wojciechk8/NVMemProg-hardware/sim/pwr/pwr_sim_csen.cir

* gnetlist -g spice-sdb -o pwr_sim_csen.cir pwr_sim_csen.sch
*********************************************************
* Spice file generated by gnetlist                      *
* spice-sdb version 4.28.2007 by SDB --                 *
* provides advanced spice netlisting capability.        *
* Documentation at http://www.brorson.com/gEDA/SPICE/   *
*********************************************************
*vvvvvvvv  Included SPICE model from LM393.cir vvvvvvvv
* LM393 VOLTAGE COMPARATOR "MACROMODEL" SUBCIRCUIT
* CREATED USING PARTS VERSION 4.03 ON 03/07/90 AT 14:17
* REV (N/A)
* CONNECTIONS:   NON-INVERTING INPUT
*                | INVERTING INPUT
*                | | POSITIVE POWER SUPPLY
*                | | | NEGATIVE POWER SUPPLY
*                | | | | OPEN COLLECTOR OUTPUT
*                | | | | |
.SUBCKT LM393    1 2 3 4 5
*
  F1    9  3 V1 1
  IEE   3  7 DC 100.0E-6
  VI1  21  1 DC .75
  VI2  22  2 DC .75
  Q1    9 21  7 QIN
  Q2    8 22  7 QIN
  Q3    9  8  4 QMO
  Q4    8  8  4 QMI
.MODEL QIN PNP(IS=800.0E-18 BF=2.000E3)
.MODEL QMI NPN(IS=800.0E-18 BF=1002)
.MODEL QMO NPN(IS=800.0E-18 BF=1000 CJC=1E-15 TR=807.4E-9)
  E1   10  4  9  4  1
  V1   10 11 DC 0
  Q5    5 11  4 QOC
.MODEL QOC NPN(IS=800.0E-18 BF=20.29E3 CJC=1E-15 TF=942.6E-12 TR=543.8E-9)
  DP    4  3 DX
  RP 3  4 46.3E3
.MODEL DX  D(IS=800.0E-18)
*
.ENDS
*^^^^^^^^  End of included SPICE model from LM393.cir ^^^^^^^^
*
*vvvvvvvv  Included SPICE model from TS912.cir vvvvvvvv
** Standard Linear Ics Macromodels, 1993.
** CONNECTIONS :
* 1 NON-INVERTING INPUT
* 2 INVERTING INPUT
* 3 POSITIVE POWER SUPPLY
* 4 NEGATIVE POWER SUPPLY
* 5 OUTPUT
.SUBCKT TS912 2 1 4 5 3
**********************************************************
.MODEL MDTH D IS=1E-8 KF=6.563355E-14 CJO=10F
* INPUT STAGE
CIP 2 5 1.500000E-12
CIN 1 5 1.500000E-12
EIP 10 5 2 5 1
EIN 16 5 1 5 1
RIP 10 11 6.500000E+00
RIN 15 16 6.500000E+00
RIS 11 15 7.655100E+00
DIP 11 12 MDTH 400E-12
DIN 15 14 MDTH 400E-12
VOFP 12 13 DC 0.000000E+00
VOFN 13 14 DC 0
IPOL 13 5 4.000000E-05
CPS 11 15 3.82E-08
DINN 17 13 MDTH 400E-12
VIN 17 5 -0.5000000e+00
DINR 15 18 MDTH 400E-12
VIP 4 18 -0.5000000E+00
FCP 4 5 VOFP 7.750000E+00
FCN 5 4 VOFN 7.750000E+00
* AMPLIFYING STAGE
FIP 5 19 VOFP 5.500000E+02
FIN 5 19 VOFN 5.500000E+02
RG1 19 5 5.087344E+05
RG2 19 4 5.087344E+05
CC 19 29 2.200000E-08
HZTP 30 29 VOFP 12.33E+02
HZTN  5 30 VOFN 12.33E+02
DOPM 19 22 MDTH 400E-12
DONM 21 19 MDTH 400E-12
HOPM 22 28 VOUT 3135
VIPM 28 4 150
HONM 21 27 VOUT 3135
VINM 5 27 150
EOUT 26 23 19 5 1
VOUT 23 5 0
ROUT 26 3 65
COUT 3 5 1.000000E-12
DOP 19 68 MDTH 400E-12
VOP 4 25 1.924
HSCP 68 25 VSCP1 1E8
DON 69 19 MDTH 400E-12
VON 24 5 2.4419107
HSCN 24 69 VSCN1 1.5E8
VSCTHP 60 61 0.1375
DSCP1 61 63 MDTH 400E-12
VSCP1 63 64 0
ISCP 64 0 1.000000E-8
DSCP2 0 64 MDTH 400E-12
DSCN2 0 74 MDTH 400E-12
ISCN 74 0 1.000000E-8
VSCN1 73 74 0
DSCN1 71 73 MDTH 400E-12
VSCTHN 71 70 -0.75
ESCP 60 0 2 1 500
ESCN 70 0 2 1 -2000
.ENDS
*^^^^^^^^  End of included SPICE model from TS912.cir ^^^^^^^^
*
*==============  Begin SPICE netlist of main design ============
Vcset cset 0 DC 0.25
Vload ctrl_load 0 pwl 0ms 200 4ms 50
* begin vcvs expansion, e<name>
Eload LOAD 0 unconnected_pin-1 unconnected_pin-2 VALUE={i(Vout)*v(ctrl_load)}
Isense_Eload unconnected_pin-1 unconnected_pin-2 dc 0
IOut_Eload LOAD 0 dc 0
* end vcvs expansion
R4 DIFF_OUT 3 39k  
R2 0 2 39k  
XU1 2 3 VCC 0 DIFF_OUT TS912
Vout 1 LOAD DC 0V
R110 #OCPROT VCC 10k  
XU3 cset DIFF_OUT VCC 0 #OCPROT LM393
R3 3 1 1.2k  
R1 2 VCC 1.2k  
Rcs VCC 1 180m  
V2 VCC 0 DC 5V
.OPTIONS ABSTOL=1nA VNTOL=1uV CHGTOL=1pC ITL1=150 ITL2=150 ITL4=500 RELTOL=0.001

.CONTROL
  *OP
  TRAN 0.1u 4m uic
  PLOT V(cset) V(DIFF_OUT) I(Vout) V(#OCPROT)
  meas tran yeval FIND i(Vout) WHEN v(#OCPROT)=4.5 FALL=1
.ENDC

.end
