wojciechk8/NVMemProg-hardware/sim/pwr/pwr_sim_fpga_sw.cir

* gnetlist -g spice-sdb -o pwr_sim_fpga_sw.cir pwr_sim_fpga_sw.sch
*********************************************************
* Spice file generated by gnetlist                      *
* spice-sdb version 4.28.2007 by SDB --                 *
* provides advanced spice netlisting capability.        *
* Documentation at http://www.brorson.com/gEDA/SPICE/   *
*********************************************************
*vvvvvvvv  Included SPICE model from LM393.cir vvvvvvvv
* LM393 VOLTAGE COMPARATOR "MACROMODEL" SUBCIRCUIT
* CREATED USING PARTS VERSION 4.03 ON 03/07/90 AT 14:17
* REV (N/A)
* CONNECTIONS:   NON-INVERTING INPUT
*                | INVERTING INPUT
*                | | POSITIVE POWER SUPPLY
*                | | | NEGATIVE POWER SUPPLY
*                | | | | OPEN COLLECTOR OUTPUT
*                | | | | |
.SUBCKT LM393    1 2 3 4 5
*
  F1    9  3 V1 1
  IEE   3  7 DC 100.0E-6
  VI1  21  1 DC .75
  VI2  22  2 DC .75
  Q1    9 21  7 QIN
  Q2    8 22  7 QIN
  Q3    9  8  4 QMO
  Q4    8  8  4 QMI
.MODEL QIN PNP(IS=800.0E-18 BF=2.000E3)
.MODEL QMI NPN(IS=800.0E-18 BF=1002)
.MODEL QMO NPN(IS=800.0E-18 BF=1000 CJC=1E-15 TR=807.4E-9)
  E1   10  4  9  4  1
  V1   10 11 DC 0
  Q5    5 11  4 QOC
.MODEL QOC NPN(IS=800.0E-18 BF=20.29E3 CJC=1E-15 TF=942.6E-12 TR=543.8E-9)
  DP    4  3 DX
  RP 3  4 46.3E3
.MODEL DX  D(IS=800.0E-18)
*
.ENDS
*^^^^^^^^  End of included SPICE model from LM393.cir ^^^^^^^^
*
*vvvvvvvv  Included SPICE model from OptiMOS2_20V.lib vvvvvvvv

*****************************************************************
* INFINEON Power Transistors                                    *
* Level-1 / 3 SPICE Library for OptiMOS/OptiMOS2 n-Channel      *
* Transistors (20V)                                             *
* Version 240715                                                *
*                                                               *
*****************************************************************
*                                                               *
* The Simulation Model is subject to change without notice. In  *
* addition, models can be a useful tool in evaluating device    *
* performance, they cannot reflect the accurate device          *
* performance under all conditions, nor are they intended to    *
* replace bread boarding for final verification. Infineon       *
* therefore does not assume any warranty or liability           *
* whatsoever arising from their use. Infineon does not assume   *
* any warranty or liability for the values and functions of the *
* Simulation Model.                                             *
* The methods and results of the Simulation Model are to the    *
* best of our knowledge                                         *
* correct. However, the user is fully responsible to verify and *
* validate these results under the operating conditions and in  *
* the environment of its application. Infineon will not bear    *
* the responsibility arising out of or in connection with any   *
* malfunction of the Simulation Models.                         *
* Models provided by Infineon are not warranted by Infineon as  *
* completely and comprehensively representing all the           *
* specifications and operating characteristics of the           *
* semiconductor products to which these models relate. The      *
* models describe the characteristics of typical devices. In    *
* all cases, the current data sheet information for a given     *
* device is the conclusive design guideline and the only actual * 
* performance specification.                                    *
*                                                               *
*                                                               *
* This library contains models of the following INFINEON        *
* OptiMOS/OptiMOS2 transistors:                                 *
*                                                               *
*  OptiMOS2 20V ULL, 1.8 V rated                                *
* BSR802N                                                       *
* BSL802SN                                                      *
* BSL806N  (L3 modeled as single only)                          *
* BSS806N                                                       *
* BSS806NE                                                      *
* BSS816NW                                                      * 
* BSD816SN                                                      *
* BSD840N  (L3 modeled as single only)                          *
*                                                               *
*   OptiMOS2 20V SLL, (2.5 V rated)                             *
* BSC019N02KS                                                   *
* BSC026N02KS                                                   *
* BSC046N02KS                                                   *
* BSR202N                                                       *
* BSL202SN                                                      *
* BSO330N02K                                                    *
* BSL205N  (L3 modeled as single only)                          *
* BSL207N  (L3 modeled as single only)                          *
* BSL214N  (L3 modeled as single only)                          *
* BSS205N                                                       *
* BSS214N                                                       *
* BSS214NW                                                      *
* BSD235N  (L3 modeled as single only)                          *
* BSD214SN                                                      *
*                                                               *
*****************************************************************
* thermal nodes of level 3 models:                              *
*                                                               *
*  .SUBCKT IPP05N03LA drain gate source Tj Tcase                *
*  Tj :    potential=temperature (in ?C) at junction (typically *
*          not connected)                                       *
*  Tcase : node where the boundary contition - external heat    *
*          sinks etc - have to be connected (ideal heat sink    *
*          can be modeled by using a voltage source stating the *
*          ambient temperature in ?C between Tcase and ground.  *
*                                                               *
*****************************************************************

.SUBCKT S3_20_s_var dd g s0 Tj PARAMS: a=1 dVth=0 dR=0 dgfs=0 Inn=1 Unn=1 Rmax=1
+gmin=1 Rs=1 Rp=1 dC=0 Rm=1u heat=0

.PARAM  Fm=0.07      Fn=0.5       kbq=85.8u
.PARAM  c=1          muc=0.0      Vth0=1.628   auth=1.481m   al=0.5
.PARAM  UT=100m      ab=24.7m     ab2=0        lB=-23        UB=25.37

.PARAM  b0=128.9     p0=2.714     p1=-6.3m     p2=13u

.PARAM  Rd=8.3m      nmu=2.7      Tref=298     T0=273       lnIsj=-22.24
.PARAM  ndi=1.218    Rdi=6.36m    nmu2=0.032   ta=3n        td=20n
.PARAM  Rf=0.6       nmu3=1.5    

.PARAM  f1=380p      f2=400p      f3=830p      U0=3       nc=0.5    nd=0.5
.PARAM  g1=11        bb=0.4       remp=5p      f2r=100p

.PARAM  Vmin=1.378   Vmax=1.878  dCmax=0.33
.PARAM  Vth={Vth0+(Vmax-Vth0)*limit(dVth,0,1)-(Vmin-Vth0)*limit(dVth,-1,0)}
.PARAM  q0={b0*((T0/Tref)**nmu3)*a}
.PARAM  q1={(Unn-Inn*Rs-Vth0)*q0}
.PARAM  q2={(Fm*SQRT(0.4)-c)*Inn*q0}
.PARAM  Rlim={(q1+2*q2*Rmax-SQRT(q1**2+4*q2))/(2*q2)}
.PARAM  dRd={Rd/a+if(dVth==0,limit(dR,0,1)*max(Rlim-Rd/a-Rs-Rp,0),0)}
.PARAM  bm={c/((1/gmin-Rs)**2*Inn*a*(T0/Tref)**nmu3)}
.PARAM  bet={b0+(b0-bm)*if(dR==0,if(dVth==0,limit(dgfs,-1,0),0),0)}
.PARAM  dC1={1+dCmax*limit(dC,0,1)}
.PARAM  dC2={1+dCmax*limit(dC,0,1)*1.5}

.PARAM  Cox={f1*a*dC2}
.PARAM  Cox1={remp*SQRT(a)*dC2}
.PARAM  Cds0={(f2*a+f2r*SQRT(a))*dC1}
.PARAM  Cgs0={f3*a*dC1}
.PARAM  dRdi={Rdi/a}

.FUNC  I0(Uee,p,pp,z1,cc)  {if(Uee>pp,(Uee-cc*z1)*z1,p*(pp-p)/cc*exp((Uee-pp)/p))}
.FUNC  Ig(Uds,T,p,Uee,cc)  {bet*(T0/T)**nmu3*I0(Uee,p,min(2*p,p+cc*Uds),min(Uds,Uee/(2*cc)),cc)}
.FUNC  J(d,g,T,da,s) 
+ {a*s*((Ig(da,T,(p0+(p1+p2*T)*T)*kbq*T,g-Vth+auth*(T-Tref)+Fm*da**Fn,c*(T/Tref)**muc)+exp(min(lB+(d-UB-ab*(T-Tref))/UT,25))))}

.FUNC  Idiode(Usd,Tj,Iss) {exp(min(log(Iss)+Usd/(ndi*kbq*Tj),7))-Iss}
.FUNC  Idiod(Usd,Tj)      {a*Idiode(Usd,Tj,exp(min(lnIsj+(Tj/Tref-1)*1.12/(ndi*kbq*Tj),7))*(Tj/Tref)**1)}

E_Edg     d   ox  VALUE {max(V(d,g),-bb)-(1/(g1*(1-nc))*((1/(1+g1*max(V(d,g)+bb,0)))**(nc-1)-(1/(1+g1*bb))**(nc-1)))}
C_Cdg    ox    g  {Cox}
Vx        d   ox1 0
C_Cdg1   ox1   g  {Cox1}

E_Eds     d edep  VALUE {(V(d,s)-I(V_sense3)/Cds0)}
C_Cds  edep    s  {Cds0}

C_Cgs   g    s   {Cgs0}


G_chan    d    s  VALUE={J(V(d,s),V(g,s),T0+limit(V(Tj),-200,300),(SQRT(1+4*al*abs(V(d,s)))-1)/2/al,sgn(V(d,s)))}
G_RMos   d1    d  VALUE={V(d1,d)/(Rf*dRd+(1-Rf)*dRd*((limit(V(Tj),-200,999)+T0)/Tref)**nmu)}
V_sense  dd   d1  0
G_diode   s   d3  VALUE={Idiod(V(s,d3),T0+limit(V(Tj),-200,499))}
G_Rdio   d2   d1  VALUE={V(d2,d1)/(dRdi*((limit(V(Tj),-200,999)+T0)/Tref)**nmu2)}
V_sense2 d2   d3  0

L_L001    a    c  {td/(ta+td)}
R_R001    a    b  {1/ta}
V_sense3  c    0  0
E_E001    b    0  VALUE {I(V_sense2)}
E_E002    e    0  VALUE {Cds0*1/(1-nd)*U0**nd*(limit(U0+V(d1,s),0,2*UB))**(1-nd)}
R_R002    e    c  1
R_R003    a    0  500Meg

R1        g    s  1G
Rd01      d    s  500Meg
Rd02     d2    s  500Meg
Rd03     d1    d  1k

Rmet      s    s0 {Rm}

G_TH      0   Tj  VALUE =
+{(LIMIT(I(V_sense2)*V(d1,s)+(V(s,s0)**2)/Rm+(I(V_sense)-I(V_sense2))*V(d1,d)+
+(I(V_sense)-I(V_sense2)-I(E_Edg)-I(Vx)-I(E_Eds))*V(d,s),-10k,100k))}

.ENDS

**********

.SUBCKT S3_20_u_var dd g s0 Tj PARAMS: a=1 dVth=0 dR=0 dgfs=0 Inn=1 Unn=1 Rmax=1
+gmin=1 Rs=1 Rp=1 dC=0 Rm=1u heat=0

.PARAM  Fm=0.025     Fn=0.5       kbq=85.8u
.PARAM  c=0.75       muc=0.0      Vth0=1.17    auth=1.36m    al=0.001
.PARAM  UT=100m      ab=22m       ab2=0        lB=-23        UB=24.2

.PARAM  b0=180       p0=2.61      p1=-6.93m    p2=12.5u

.PARAM  Rd=6.642m    nmu=3.045    Tref=298     T0=273       lnIsj=-22.24
.PARAM  ndi=1.218    Rdi=6.36m    nmu2=0.032   ta=3n        td=20n
.PARAM  Rf=0.723     nmu3=1.5    

.PARAM  f1=700p      f2=400p      f3=970p      U0=3         nc=0.5    nd=0.5
.PARAM  g1=21        bb=0.11      remp=4p      f2r=100p

.PARAM  Vmin=0.97    Vmax=1.37    dCmax=0.33
.PARAM  Vth={Vth0+(Vmax-Vth0)*limit(dVth,0,1)-(Vmin-Vth0)*limit(dVth,-1,0)}
.PARAM  q0={b0*((T0/Tref)**nmu3)*a}
.PARAM  q1={(Unn-Inn*Rs-Vth0)*q0}
.PARAM  q2={(Fm*SQRT(0.4)-c)*Inn*q0}
.PARAM  Rlim={(q1+2*q2*Rmax-SQRT(q1**2+4*q2))/(2*q2)}
.PARAM  dRd={Rd/a+if(dVth==0,limit(dR,0,1)*max(Rlim-Rd/a-Rs-Rp,0),0)}
.PARAM  bm={c/((1/gmin-Rs)**2*Inn*a*(T0/Tref)**nmu3)}
.PARAM  bet={b0+(b0-bm)*if(dR==0,if(dVth==0,limit(dgfs,-1,0),0),0)}
.PARAM  dC1={1+dCmax*limit(dC,0,1)}
.PARAM  dC2={1+dCmax*limit(dC,0,1)*1.5}

.PARAM  Cox={f1*a*dC2}
.PARAM  Cox1={remp*SQRT(a)*dC2}
.PARAM  Cds0={(f2*a+f2r*SQRT(a))*dC1}
.PARAM  Cgs0={f3*a*dC1}
.PARAM  dRdi={Rdi/a}

.FUNC  I0(Uee,p,pp,z1,cc)  {if(Uee>pp,(Uee-cc*z1)*z1,p*(pp-p)/cc*exp((Uee-pp)/p))}
.FUNC  Ig(Uds,T,p,Uee,cc)  {bet*(T0/T)**nmu3*I0(Uee,p,min(2*p,p+cc*Uds),min(Uds,Uee/(2*cc)),cc)}
.FUNC  J(d,g,T,da,s) 
+ {a*s*((Ig(da,T,(p0+(p1+p2*T)*T)*kbq*T,g-Vth+auth*(T-Tref)+Fm*da**Fn,c*(T/Tref)**muc)+exp(min(lB+(d-UB-ab*(T-Tref))/UT,25))))}

.FUNC  Idiode(Usd,Tj,Iss) {exp(min(log(Iss)+Usd/(ndi*kbq*Tj),7))-Iss}
.FUNC  Idiod(Usd,Tj)      {a*Idiode(Usd,Tj,exp(min(lnIsj+(Tj/Tref-1)*1.12/(ndi*kbq*Tj),7))*(Tj/Tref)**1)}

E_Edg     d   ox  VALUE {max(V(d,g),-bb)-(1/(g1*(1-nc))*((1/(1+g1*max(V(d,g)+bb,0)))**(nc-1)-(1/(1+g1*bb))**(nc-1)))}
C_Cdg    ox    g  {Cox}
Vx        d   ox1 0
C_Cdg1   ox1   g  {Cox1}

E_Eds     d edep  VALUE {(V(d,s)-I(V_sense3)/Cds0)}
C_Cds  edep    s  {Cds0}

C_Cgs   g    s   {Cgs0}


G_chan    d    s  VALUE={J(V(d,s),V(g,s),T0+limit(V(Tj),-200,300),(SQRT(1+4*al*abs(V(d,s)))-1)/2/al,sgn(V(d,s)))}
G_RMos   d1    d  VALUE={V(d1,d)/(Rf*dRd+(1-Rf)*dRd*((limit(V(Tj),-200,999)+T0)/Tref)**nmu)}
V_sense  dd   d1  0
G_diode   s   d3  VALUE={Idiod(V(s,d3),T0+limit(V(Tj),-200,499))}
G_Rdio   d2   d1  VALUE={V(d2,d1)/(dRdi*((limit(V(Tj),-200,999)+T0)/Tref)**nmu2)}
V_sense2 d2   d3  0

L_L001    a    c  {td/(ta+td)}
R_R001    a    b  {1/ta}
V_sense3  c    0  0
E_E001    b    0  VALUE {I(V_sense2)}
E_E002    e    0  VALUE {Cds0*1/(1-nd)*U0**nd*(limit(U0+V(d1,s),0,2*UB))**(1-nd)}
R_R002    e    c  1
R_R003    a    0  500Meg

R1        g    s  1G
Rd01      d    s  500Meg
Rd02     d2    s  500Meg
Rd03     d1    d  1k

Rmet      s    s0 {Rm}

G_TH      0   Tj  VALUE =
+{(LIMIT(I(V_sense2)*V(d1,s)+(V(s,s0)**2)/Rm+(I(V_sense)-I(V_sense2))*V(d1,d)+
+(I(V_sense)-I(V_sense2)-I(E_Edg)-I(Vx)-I(E_Eds))*V(d,s),-10k,100k))}

.ENDS

****************************************************************************************************

.SUBCKT BSC019N02KS drain gate source Tj Tcase PARAMS: dVth=0 dRdson=0 dgfs=0 dC=0 Zthtype=0 Ls=1n Ld=1n Lg=3n

.PARAM Rs=482u      Rg=1.9       Rd=50u       Rm=400u
.PARAM Inn=50       Unn=4.5      Rmax=1.95m   gmin=100

.PARAM act=11.03



X1  d1 g s Tj S3_20_s_var PARAMS: a={act} dVth={dVth} dR={dRdson} dgfs={dgfs} Inn={Inn} Unn={Unn} 
                                        +Rmax={Rmax} gmin={gmin} Rs={Rs} Rp={Rd} dC={dC} Rm={Rm}
Rg    g1     g    {Rg}   
Lg    gate   g1   {Lg*if(dgfs==99,0,1)}
Gs    s1     s    VALUE={V(s1,s)/(Rs*(1+(limit(V(Tj),-200,999)-25)*4m)-Rm)}
Rsa   s1     s    1Meg
Ls    source s1   {Ls*if(dgfs==99,0,1)}
Rda   d1     d2   {Rd}
Ld    drain  d2   {Ld*if(dgfs==99,0,1)}
RLs   source s1   10
RLg   gate   g1   10
RLd   drain  d2   10




Rth1  Tj      t1              {2.39m+limit(Zthtype,0,1)*878.98u}
Rth2  t1      t2              {32.13m+limit(Zthtype,0,1)*11.89m}
Rth3  t2      t3              {123.34m+limit(Zthtype,0,1)*39.62m}
Rth4  t3      t4              {129.59m+limit(Zthtype,0,1)*217.61m}
Rth5  t4      Tcase           {239.83m+limit(Zthtype,0,1)*402.72m}
Cth1  Tj      0               76.781u
Cth2  t1      0               435.464u
Cth3  t2      0               2.72m
Cth4  t3      0               1.944m
Cth5  t4      0               47.017m
Cth6  Tcase   0               30m

.ENDS

**********

.SUBCKT BSC026N02KS drain gate source Tj Tcase PARAMS: dVth=0 dRdson=0 dgfs=0 dC=0 Zthtype=0 Ls=1n Ld=1n Lg=3n

.PARAM Rs=361u      Rg=1.5       Rd=50u       Rm=190u
.PARAM Inn=50       Unn=4.5      Rmax=2.6m    gmin=57

.PARAM act=6.77



X1  d1 g s Tj S3_20_s_var PARAMS: a={act} dVth={dVth} dR={dRdson} dgfs={dgfs} Inn={Inn} Unn={Unn} 
                                        +Rmax={Rmax} gmin={gmin} Rs={Rs} Rp={Rd} dC={dC} Rm={Rm}
Rg    g1     g    {Rg}   
Lg    gate   g1   {Lg*if(dgfs==99,0,1)}
Gs    s1     s    VALUE={V(s1,s)/(Rs*(1+(limit(V(Tj),-200,999)-25)*4m)-Rm)}
Rsa   s1     s    1Meg
Ls    source s1   {Ls*if(dgfs==99,0,1)}
Rda   d1     d2   {Rd}
Ld    drain  d2   {Ld*if(dgfs==99,0,1)}
RLs   source s1   10
RLg   gate   g1   10
RLd   drain  d2   10




Rth1  Tj      t1              {3.89m+limit(Zthtype,0,1)*1.44m}
Rth2  t1      t2              {51.65m+limit(Zthtype,0,1)*19.11m}
Rth3  t2      t3              {186.29m+limit(Zthtype,0,1)*64.8m}
Rth4  t3      t4              {211.13m+limit(Zthtype,0,1)*300.99m}
Rth5  t4      Tcase           {313.61m+limit(Zthtype,0,1)*447.09m}
Cth1  Tj      0               47.127u
Cth2  t1      0               270.877u
Cth3  t2      0               1.834m
Cth4  t3      0               1.193m
Cth5  t4      0               33.557m
Cth6  Tcase   0               35m

.ENDS

**********

.SUBCKT BSC046N02KS drain gate source Tj Tcase PARAMS: dVth=0 dRdson=0 dgfs=0 dC=0 Zthtype=0 Ls=1n Ld=1n Lg=3n

.PARAM Rs=254u      Rg=1.9       Rd=50u       Rm=83u
.PARAM Inn=50       Unn=4.5      Rmax=4.6m    gmin=42

.PARAM act=3.55



X1  d1 g s Tj S3_20_s_var PARAMS: a={act} dVth={dVth} dR={dRdson} dgfs={dgfs} Inn={Inn} Unn={Unn} 
                                        +Rmax={Rmax} gmin={gmin} Rs={Rs} Rp={Rd} dC={dC} Rm={Rm}
Rg    g1     g    {Rg}   
Lg    gate   g1   {Lg*if(dgfs==99,0,1)}
Gs    s1     s    VALUE={V(s1,s)/(Rs*(1+(limit(V(Tj),-200,999)-25)*4m)-Rm)}
Rsa   s1     s    1Meg
Ls    source s1   {Ls*if(dgfs==99,0,1)}
Rda   d1     d2   {Rd}
Ld    drain  d2   {Ld*if(dgfs==99,0,1)}
RLs   source s1   10
RLg   gate   g1   10
RLd   drain  d2   10




Rth1  Tj      t1              {7.41m+limit(Zthtype,0,1)*2.75m}
Rth2  t1      t2              {96.23m+limit(Zthtype,0,1)*35.61m}
Rth3  t2      t3              {343.77m+limit(Zthtype,0,1)*124.41m}
Rth4  t3      t4              {402.63m+limit(Zthtype,0,1)*574.54m}
Rth5  t4      Tcase           {417.25m+limit(Zthtype,0,1)*595.4m}
Cth1  Tj      0               24.712u
Cth2  t1      0               145.39u
Cth3  t2      0               1.004m
Cth4  t3      0               625.577u
Cth5  t4      0               25.139m
Cth6  Tcase   0               40m

.ENDS

**********

.SUBCKT BSR202N drain gate source Tj Tcase PARAMS: dVth=0 dRdson=0 dgfs=0 dC=0 Zthtype=0 Ls=0.8n Ld=1n Lg=3n

.PARAM Rs=4.48m     Rg=1.9       Rd=500u      Rm=4m
.PARAM Inn=3.8      Unn=4.5      Rmax=23m     gmin=8

.PARAM act=0.991



X1  d1 g s Tj S3_20_s_var PARAMS: a={act} dVth={dVth} dR={dRdson} dgfs={dgfs} Inn={Inn} Unn={Unn} 
                                        +Rmax={Rmax} gmin={gmin} Rs={Rs} Rp={Rd} dC={dC} Rm={Rm}
Rg    g1     g    {Rg}   
Lg    gate   g1   {Lg*if(dgfs==99,0,1)}
Gs    s1     s    VALUE={V(s1,s)/(Rs*(1+(limit(V(Tj),-200,999)-25)*4m)-Rm)}
Rsa   s1     s    1Meg
Ls    source s1   {Ls*if(dgfs==99,0,1)}
Rda   d1     d2   {Rd}
Ld    drain  d2   {Ld*if(dgfs==99,0,1)}
RLs   source s1   10
RLg   gate   g1   10
RLd   drain  d2   10




Rth1  Tj      t1              {26.69m+limit(Zthtype,0,1)*9.88m}
Rth2  t1      t2              {321.74m+limit(Zthtype,0,1)*119.08m}
Rth3  t2      t3              {1.48+limit(Zthtype,0,1)*451.64m}
Rth4  t3      t4              {42.78+limit(Zthtype,0,1)*37.73}
Rth5  t4      Tcase           {30.33+limit(Zthtype,0,1)*26.75}
Cth1  Tj      0               6.864u
Cth2  t1      0               43.483u
Cth3  t2      0               141.188u
Cth4  t3      0               1.166m
Cth5  t4      0               9.189m
Cth6  Tcase   0               5m

.ENDS

**********

.SUBCKT BSL202SN drain gate source Tj Tcase PARAMS: dVth=0 dRdson=0 dgfs=0 dC=0 Zthtype=0 Ls=1n Ld=1n Lg=3n

.PARAM Rs=5.48m     Rg=1.9       Rd=140u      Rm=5m
.PARAM Inn=3.8      Unn=4.5      Rmax=24m     gmin=8

.PARAM act=0.991



X1  d1 g s Tj S3_20_s_var PARAMS: a={act} dVth={dVth} dR={dRdson} dgfs={dgfs} Inn={Inn} Unn={Unn} 
                                        +Rmax={Rmax} gmin={gmin} Rs={Rs} Rp={Rd} dC={dC} Rm={Rm}
Rg    g1     g    {Rg}   
Lg    gate   g1   {Lg*if(dgfs==99,0,1)}
Gs    s1     s    VALUE={V(s1,s)/(Rs*(1+(limit(V(Tj),-200,999)-25)*4m)-Rm)}
Rsa   s1     s    1Meg
Ls    source s1   {Ls*if(dgfs==99,0,1)}
Rda   d1     d2   {Rd}
Ld    drain  d2   {Ld*if(dgfs==99,0,1)}
RLs   source s1   10
RLg   gate   g1   10
RLd   drain  d2   10




Rth1  Tj      t1              {26.56m+limit(Zthtype,0,1)*9.83m}
Rth2  t1      t2              {320.25m+limit(Zthtype,0,1)*118.52m}
Rth3  t2      t3              {1.93+limit(Zthtype,0,1)*459.59m}
Rth4  t3      t4              {10.69+limit(Zthtype,0,1)*11.84}
Rth5  t4      Tcase           {11.67+limit(Zthtype,0,1)*12.93}
Cth1  Tj      0               6.898u
Cth2  t1      0               43.687u
Cth3  t2      0               145.816u
Cth4  t3      0               635.538u
Cth5  t4      0               7m


.ENDS

*********************


.SUBCKT BSL205N drain gate source Tj Tcase PARAMS: dVth=0 dRdson=0 dgfs=0 dC=0 Zthtype=0 Ls=1n Ld=0.5n Lg=2n

.PARAM Rs=7.13m     Rg=4.9       Rd=550u      Rm=600u
.PARAM Inn=2.5      Unn=4.5      Rmax=50m     gmin=4.6

.PARAM act=0.361



X1  d1 g s Tj S3_20_s_var PARAMS: a={act} dVth={dVth} dR={dRdson} dgfs={dgfs} Inn={Inn} Unn={Unn} 
                                        +Rmax={Rmax} gmin={gmin} Rs={Rs} Rp={Rd} dC={dC} Rm={Rm}
Rg    g1     g    {Rg}   
Lg    gate   g1   {Lg*if(dgfs==99,0,1)}
Gs    s1     s    VALUE={V(s1,s)/(Rs*(1+(limit(V(Tj),-200,999)-25)*4m)-Rm)}
Rsa   s1     s    1Meg
Ls    source s1   {Ls*if(dgfs==99,0,1)}
Rda   d1     d2   {Rd}
Ld    drain  d2   {Ld*if(dgfs==99,0,1)}
RLs   source s1   10
RLg   gate   g1   10
RLd   drain  d2   10




Rth1  Tj      t1              {72.91m+limit(Zthtype,0,1)*26.98m}
Rth2  t1      t2              {796.9m+limit(Zthtype,0,1)*294.92m}
Rth3  t2      t3              {4.09+limit(Zthtype,0,1)*1.28}
Rth4  t3      t4              {19.18+limit(Zthtype,0,1)*7.1}
Rth5  t4      Tcase           {49.02+limit(Zthtype,0,1)*18.14}
Cth1  Tj      0               2.513u
Cth2  t1      0               6.514u
Cth3  t2      0               50.593u
Cth4  t3      0               214.138u
Cth5  t4      0               1.193m
Cth6  Tcase   0               5m

.ENDS

**********

.SUBCKT BSS205N drain gate source Tj Tcase PARAMS: dVth=0 dRdson=0 dgfs=0 dC=0 Zthtype=0 Ls=1n Ld=0.5n Lg=2n

.PARAM Rs=8.11m     Rg=4.9       Rd=550u      Rm=600u
.PARAM Inn=2.5      Unn=4.5      Rmax=50m     gmin=4.6

.PARAM act=0.361



X1  d1 g s Tj S3_20_s_var PARAMS: a={act} dVth={dVth} dR={dRdson} dgfs={dgfs} Inn={Inn} Unn={Unn} 
                                        +Rmax={Rmax} gmin={gmin} Rs={Rs} Rp={Rd} dC={dC} Rm={Rm}
Rg    g1     g    {Rg}   
Lg    gate   g1   {Lg*if(dgfs==99,0,1)}
Gs    s1     s    VALUE={V(s1,s)/(Rs*(1+(limit(V(Tj),-200,999)-25)*4m)-Rm)}
Rsa   s1     s    1Meg
Ls    source s1   {Ls*if(dgfs==99,0,1)}
Rda   d1     d2   {Rd}
Ld    drain  d2   {Ld*if(dgfs==99,0,1)}
RLs   source s1   10
RLg   gate   g1   10
RLd   drain  d2   10




Rth1  Tj      t1              {72.91m+limit(Zthtype,0,1)*26.98m}
Rth2  t1      t2              {796.9m+limit(Zthtype,0,1)*294.92m}
Rth3  t2      t3              {4.09+limit(Zthtype,0,1)*1.28}
Rth4  t3      t4              {11.88+limit(Zthtype,0,1)*11.21}
Rth5  t4      Tcase           {56.78+limit(Zthtype,0,1)*53.57}
Cth1  Tj      0               2.513u
Cth2  t1      0               6.514u
Cth3  t2      0               50.593u
Cth4  t3      0               389.69u
Cth5  t4      0               600u
Cth6  Tcase   0               6m

.ENDS

**********

.SUBCKT BSL207N drain gate source Tj Tcase PARAMS: dVth=0 dRdson=0 dgfs=0 dC=0 Zthtype=0 Ls=1.5n Ld=0.5n Lg=2n

.PARAM Rs=25.7m     Rg=4.9       Rd=550u      Rm=1m
.PARAM Inn=2.05     Unn=4.5      Rmax=70m     gmin=3.9

.PARAM act=0.361



X1  d1 g s Tj S3_20_s_var PARAMS: a={act} dVth={dVth} dR={dRdson} dgfs={dgfs} Inn={Inn} Unn={Unn} 
                                        +Rmax={Rmax} gmin={gmin} Rs={Rs} Rp={Rd} dC={dC} Rm={Rm}
Rg    g1     g    {Rg}   
Lg    gate   g1   {Lg*if(dgfs==99,0,1)}
Gs    s1     s    VALUE={V(s1,s)/(Rs*(1+(limit(V(Tj),-200,999)-25)*4m)-Rm)}
Rsa   s1     s    1Meg
Ls    source s1   {Ls*if(dgfs==99,0,1)}
Rda   d1     d2   {Rd}
Ld    drain  d2   {Ld*if(dgfs==99,0,1)}
RLs   source s1   10
RLg   gate   g1   10
RLd   drain  d2   10




Rth1  Tj      t1              {72.91m+limit(Zthtype,0,1)*26.98m}
Rth2  t1      t2              {796.9m+limit(Zthtype,0,1)*294.92m}
Rth3  t2      t3              {4.09+limit(Zthtype,0,1)*1.28}
Rth4  t3      t4              {19.18+limit(Zthtype,0,1)*7.1}
Rth5  t4      Tcase           {49.02+limit(Zthtype,0,1)*18.14}
Cth1  Tj      0               2.513u
Cth2  t1      0               6.514u
Cth3  t2      0               50.593u
Cth4  t3      0               214.138u
Cth5  t4      0               1.193m
Cth6  Tcase   0               5m

.ENDS

**********

.SUBCKT BSL214N drain gate source Tj Tcase PARAMS: dVth=0 dRdson=0 dgfs=0 dC=0 Zthtype=0 Ls=1n Ld=0.5n Lg=2n

.PARAM Rs=13.05m    Rg=11.3      Rd=550u      Rm=600u
.PARAM Inn=1.5      Unn=4.5      Rmax=140m    gmin=2.1

.PARAM act=0.122



X1  d1 g s Tj S3_20_s_var PARAMS: a={act} dVth={dVth} dR={dRdson} dgfs={dgfs} Inn={Inn} Unn={Unn} 
                                        +Rmax={Rmax} gmin={gmin} Rs={Rs} Rp={Rd} dC={dC} Rm={Rm}
Rg    g1     g    {Rg}   
Lg    gate   g1   {Lg*if(dgfs==99,0,1)}
Gs    s1     s    VALUE={V(s1,s)/(Rs*(1+(limit(V(Tj),-200,999)-25)*4m)-Rm)}
Rsa   s1     s    1Meg
Ls    source s1   {Ls*if(dgfs==99,0,1)}
Rda   d1     d2   {Rd}
Ld    drain  d2   {Ld*if(dgfs==99,0,1)}
RLs   source s1   10
RLg   gate   g1   10
RLd   drain  d2   10




Rth1  Tj      t1              {215.74m+limit(Zthtype,0,1)*79.85m}
Rth2  t1      t2              {2+limit(Zthtype,0,1)*734.81m}
Rth3  t2      t3              {7.66+limit(Zthtype,0,1)*3.92}
Rth4  t3      t4              {33.24+limit(Zthtype,0,1)*11.85}
Rth5  t4      Tcase           {59.19+limit(Zthtype,0,1)*21.11}
Cth1  Tj      0               849.255n
Cth2  t1      0               2.681u
Cth3  t2      0               16.282u
Cth4  t3      0               72.252u
Cth5  t4      0               992.905u
Cth6  Tcase   0               5m

.ENDS

**********

.SUBCKT BSS214N drain gate source Tj Tcase PARAMS: dVth=0 dRdson=0 dgfs=0 dC=0 Zthtype=0 Ls=1n Ld=0.5n Lg=2n

.PARAM Rs=15.03m    Rg=11.3      Rd=550u      Rm=600u
.PARAM Inn=1.5      Unn=4.5      Rmax=140m    gmin=2.1

.PARAM act=0.122



X1  d1 g s Tj S3_20_s_var PARAMS: a={act} dVth={dVth} dR={dRdson} dgfs={dgfs} Inn={Inn} Unn={Unn} 
                                        +Rmax={Rmax} gmin={gmin} Rs={Rs} Rp={Rd} dC={dC} Rm={Rm}
Rg    g1     g    {Rg}   
Lg    gate   g1   {Lg*if(dgfs==99,0,1)}
Gs    s1     s    VALUE={V(s1,s)/(Rs*(1+(limit(V(Tj),-200,999)-25)*4m)-Rm)}
Rsa   s1     s    1Meg
Ls    source s1   {Ls*if(dgfs==99,0,1)}
Rda   d1     d2   {Rd}
Ld    drain  d2   {Ld*if(dgfs==99,0,1)}
RLs   source s1   10
RLg   gate   g1   10
RLd   drain  d2   10




Rth1  Tj      t1              {215.74m+limit(Zthtype,0,1)*79.85m}
Rth2  t1      t2              {2+limit(Zthtype,0,1)*734.81m}
Rth3  t2      t3              {7.66+limit(Zthtype,0,1)*3.92}
Rth4  t3      t4              {11.87+limit(Zthtype,0,1)*9.08}
Rth5  t4      Tcase           {59.17+limit(Zthtype,0,1)*45.27}
Cth1  Tj      0               849.255n
Cth2  t1      0               2.681u
Cth3  t2      0               16.282u
Cth4  t3      0               223.105u
Cth5  t4      0               601.844u
Cth6  Tcase   0               6m

.ENDS

**********

.SUBCKT BSS214NW drain gate source Tj Tcase PARAMS: dVth=0 dRdson=0 dgfs=0 dC=0 Zthtype=0 Ls=1n Ld=0.5n Lg=1n

.PARAM Rs=11.28m    Rg=11.3      Rd=800u      Rm=600u
.PARAM Inn=1.5      Unn=4.5      Rmax=140m    gmin=2.1

.PARAM act=0.122



X1  d1 g s Tj S3_20_s_var PARAMS: a={act} dVth={dVth} dR={dRdson} dgfs={dgfs} Inn={Inn} Unn={Unn} 
                                        +Rmax={Rmax} gmin={gmin} Rs={Rs} Rp={Rd} dC={dC} Rm={Rm}
Rg    g1     g    {Rg}   
Lg    gate   g1   {Lg*if(dgfs==99,0,1)}
Gs    s1     s    VALUE={V(s1,s)/(Rs*(1+(limit(V(Tj),-200,999)-25)*4m)-Rm)}
Rsa   s1     s    1Meg
Ls    source s1   {Ls*if(dgfs==99,0,1)}
Rda   d1     d2   {Rd}
Ld    drain  d2   {Ld*if(dgfs==99,0,1)}
RLs   source s1   10
RLg   gate   g1   10
RLd   drain  d2   10




Rth1  Tj      t1              {215.74m+limit(Zthtype,0,1)*79.85m}
Rth2  t1      t2              {2+limit(Zthtype,0,1)*734.81m}
Rth3  t2      t3              {7.66+limit(Zthtype,0,1)*3.92}
Rth4  t3      t4              {27.56+limit(Zthtype,0,1)*23.9}
Rth5  t4      Tcase           {39.6+limit(Zthtype,0,1)*34.33}
Cth1  Tj      0               849.255n
Cth2  t1      0               2.681u
Cth3  t2      0               15.316u
Cth4  t3      0               326.936u
Cth5  t4      0               1.111m
Cth6  Tcase   0               1.8m

.ENDS

**********

.SUBCKT BSD214SN drain gate source Tj Tcase PARAMS: dVth=0 dRdson=0 dgfs=0 dC=0 Zthtype=0 Ls=1n Ld=0.5n Lg=1n

.PARAM Rs=16.37m    Rg=11.3      Rd=240u      Rm=600u
.PARAM Inn=1.5      Unn=4.5      Rmax=140m    gmin=2.1

.PARAM act=0.122



X1  d1 g s Tj S3_20_s_var PARAMS: a={act} dVth={dVth} dR={dRdson} dgfs={dgfs} Inn={Inn} Unn={Unn} 
                                        +Rmax={Rmax} gmin={gmin} Rs={Rs} Rp={Rd} dC={dC} Rm={Rm}
Rg    g1     g    {Rg}   
Lg    gate   g1   {Lg*if(dgfs==99,0,1)}
Gs    s1     s    VALUE={V(s1,s)/(Rs*(1+(limit(V(Tj),-200,999)-25)*4m)-Rm)}
Rsa   s1     s    1Meg
Ls    source s1   {Ls*if(dgfs==99,0,1)}
Rda   d1     d2   {Rd}
Ld    drain  d2   {Ld*if(dgfs==99,0,1)}
RLs   source s1   10
RLg   gate   g1   10
RLd   drain  d2   10




Rth1  Tj      t1              {215.74m+limit(Zthtype,0,1)*79.85m}
Rth2  t1      t2              {2+limit(Zthtype,0,1)*734.81m}
Rth3  t2      t3              {7.66+limit(Zthtype,0,1)*3.92}
Rth4  t3      t4              {31.58+limit(Zthtype,0,1)*12.05}
Rth5  t4      Tcase           {59.17+limit(Zthtype,0,1)*22.59}
Cth1  Tj      0               849.255n
Cth2  t1      0               2.681u
Cth3  t2      0               16.282u
Cth4  t3      0               121.071u
Cth5  t4      0               493.707u
Cth6  Tcase   0               2m

.ENDS

**********

.SUBCKT BSD235N drain gate source Tj Tcase PARAMS: dVth=0 dRdson=0 dgfs=0 dC=0 Zthtype=0 Ls=1n Ld=0.5n Lg=1n

.PARAM Rs=46.66m    Rg=10.5      Rd=960u      Rm=2m
.PARAM Inn=0.95     Unn=4.5      Rmax=350m    gmin=1.1

.PARAM act=0.053



X1  d1 g s Tj S3_20_s_var PARAMS: a={act} dVth={dVth} dR={dRdson} dgfs={dgfs} Inn={Inn} Unn={Unn} 
                                        +Rmax={Rmax} gmin={gmin} Rs={Rs} Rp={Rd} dC={dC} Rm={Rm}
Rg    g1     g    {Rg}   
Lg    gate   g1   {Lg*if(dgfs==99,0,1)}
Gs    s1     s    VALUE={V(s1,s)/(Rs*(1+(limit(V(Tj),-200,999)-25)*4m)-Rm)}
Rsa   s1     s    1Meg
Ls    source s1   {Ls*if(dgfs==99,0,1)}
Rda   d1     d2   {Rd}
Ld    drain  d2   {Ld*if(dgfs==99,0,1)}
RLs   source s1   10
RLg   gate   g1   10
RLd   drain  d2   10
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
