wojciechk8/NVMemProg-hardware/sim/pwr/pwr_sim_vcc_src.cir

* gnetlist -g spice-sdb -o pwr_sim_vcc_src.cir pwr_sim_vcc_src.sch
*********************************************************
* Spice file generated by gnetlist                      *
* spice-sdb version 4.28.2007 by SDB --                 *
* provides advanced spice netlisting capability.        *
* Documentation at http://www.brorson.com/gEDA/SPICE/   *
*********************************************************
*vvvvvvvv  Included SPICE model from mc34063.cir vvvvvvvv
*			SPICE model for MC34063
*  This uses vanilla SPICE3 syntax and will work with ngspice.
*
 ***************************************************************************
 *   Copyright (C) 2007 by Ken Sarkies                                     *
 *   ksarkies@trinity.asn.au                                               *
 *                                                                         *
 *   This is free software; you can redistribute it and/or modify          *
 *   it under the terms of the GNU General Public License as published by  *
 *   the Free Software Foundation; either version 2 of the License, or     *
 *   (at your option) any later version.                                   *
 *                                                                         *
 *   This file is distributed in the hope that it will be useful,          *
 *   but WITHOUT ANY WARRANTY; without even the implied warranty of        *
 *   MERCHANTABILITY or FITNESS FOR A PARTICULAR PURPOSE.  See the         *
 *   GNU General Public License for more details.                          *
 *                                                                         *
 *   You should have received a copy of the GNU General Public License     *
 *   along with V if not, write to the Free Software Foundation, Inc.,     *
 *   51 Franklin St, Fifth Floor, Boston, MA  02110-1301  USA.             *
 ***************************************************************************

.SUBCKT mc34063 csw esw ct comm fb vcc ipk cdr

* csw = switch BJT collector, esw = switch BJT emitter ct = timing capacitor, comm = common
* fb = feedback control, vcc = power in, ipk = peak limiting, cdr = driver BJT collector
* pin numbers match order of inputs above.

* Voltage Sources
Vlogic vp5v comm DC 5V

* Reference and feedback comparator
* The reference is at 1.25V but decreases linearly to zero for Vcc < 3.75V
Breference ref comm V=(V(vcc,comm)-1.25)*u(V(vcc,comm)-1.25)-(V(vcc,comm)-2.5)*u(V(vcc,comm)-3.75)
B1 1 comm V=u(V(ref,fb))
R6 1 cinvcontrol 10K
C6 cinvcontrol comm 10pF

* Oscillator
* Hysteresis switch to drive current into timing capacitor
R1 vp5v osc 10k
S1 osc comm ct comm swmod
.MODEL swmod SW (SW VT = 1 VH = 0.25)
* Current source to drive charge/discharge currents for the timing capacitor
Bcurrent ct comm I=-35uA+255uA*u(2.5-V(osc,comm))
* Current limiting circuit increases the charge rate of the timing capacitor
Qlimit ct ipk vcc limitQ 
.model limitQ PNP(IS=1E-12 VAF=100 BF=200 IKF=0.1 XTB=1.5 BR=4
+  CJC=4.5E-12 CJE=10E-12 RB=20 RC=0.1 RE=0.1 TR=250E-9 TF=350E-12 ITF=1 VTF=2 XTF=3)

* Differentiator to provide delays to overcome latch race conditions
Ctrigger osc delay  1pF  
Rtrigger delay comm 100K  

* Delay pulse squaring comparators plus Delay gating logic.
* inverse of positive delay transition anded with the oscillator to delay the start of
* the next high part. This is then nanded with the feedback gating signal.
Bsetgate set comm V=(1-(1-u(V(delay,comm)-1))*u(V(osc,comm)-2.5)*u(V(cinvcontrol,comm)-0.5))
* Reset is just the negative delay transition anded with the oscillator and inverted.
Bminus reset comm V=(1-u(V(delay,comm)+1)*(1-u(V(osc,comm)-2.5)))

* SR Latch
Blatch1 4 comm V=(1-V(reset,comm)*u(V(3,comm)-0.5))
R4 4 2 10K
C4 2 comm 1pF IC=1V
Blatch2 gate comm V=(1-V(set,comm)*u(V(2,comm)-0.5))
R5 gate 3 10K
C5 3 comm 1pF

* Output switch gating and drive
Bcurrentdrive currentdrive comm I=10mA-20mA*V(gate,comm)*u(V(cinvcontrol,comm)-0.5)
Qdrive cdr currentdrive swbase driverQ 
.model driverQ NPN(Bf=300 CJC=4pF CJE=8pF RB=20 RC=0.1 RE=0.1)
D2 comm currentdrive 1N914 
D1 currentdrive vcc 1N914 
.MODEL 1N914 D(Is=2.52n Rs=0.568 N=1.752 Cjo=4p M=.4 Tt=20n)
Rde swbase esw 100  
Qswitch csw swbase esw switchQ
.MODEL switchQ npn (BF=75 RB=10 RE=0.25 RC=0.25 CJE=10pF CJC=10pF)
.ends
*^^^^^^^^  End of included SPICE model from mc34063.cir ^^^^^^^^
*
*vvvvvvvv  Included SPICE model from ST_POWER_SCHOTTKY_V4.LIB vvvvvvvv
*
* File     : power_schottky_v4.LIB
* Revision : 4.0
* Date     : FEBRUARY 2016
**********************************************************************
*Please Read Carefully:
*Information in this document is provided solely in connection with ST products.
*STMicroelectronics NV and its subsidiaries (?ST?) reserve the right to make :
*changes, corrections, modifications or improvements, to this document,
*and the products and services described herein at any time, without notice.
*All ST products are sold pursuant to ST?s terms and conditions of sale.
*Purchasers are solely responsible for the choice, selection and use of the ST products, and services described herein,
*and ST assumes no liability whatsoever relating to the choice, selection or use of the ST products and services described herein.
*No license, express or implied, by estoppel or otherwise, to any intellectual property rights is granted under this document.
*If any part of this document refers to any third party products or
*services it shall not be deemed a license grant by ST for the use of such third party products or
*services, or any intellectual property contained therein or
*considered as a warranty covering the use in any manner whatsoever of such third party products or
*services or any intellectual property contained therein.
*UNLESS OTHERWISE SET FORTH IN ST?S TERMS AND CONDITIONS OF SALE ST DISCLAIMS ANY EXPRESS OR IMPLIED
*WARRANTY WITH RESPECT TO THE USE AND/OR SALE OF ST PRODUCTS INCLUDING WITHOUT LIMITATION IMPLIED
*WARRANTIES OF MERCHANTABILITY, FITNESS FOR A PARTICULAR PURPOSE (AND THEIR EQUIVALENTS UNDER THE LAWS
*OF ANY JURISDICTION), OR INFRINGEMENT OF ANY PATENT, COPYRIGHT OR OTHER INTELLECTUAL PROPERTY RIGHT.
*UNLESS EXPRESSLY APPROVED IN WRITING BY AN AUTHORIZED ST REPRESENTATIVE, ST PRODUCTS ARE NOT
*RECOMMENDED, AUTHORIZED OR WARRANTED FOR USE IN MILITARY, AIR CRAFT, SPACE, LIFE SAVING, OR LIFE SUSTAINING
*APPLICATIONS, NOR IN PRODUCTS OR SYSTEMS WHERE FAILURE OR MALFUNCTION MAY RESULT IN PERSONAL INJURY,
*DEATH, OR SEVERE PROPERTY OR ENVIRONMENTAL DAMAGE. ST PRODUCTS WHICH ARE NOT SPECIFIED AS "AUTOMOTIVE
*GRADE" MAY ONLY BE USED IN AUTOMOTIVE APPLICATIONS AT USER?S OWN RISK.
*Resale of ST products with provisions different from the statements and/or technical features
*set forth in this document shall immediately void any warranty granted by ST for the ST product or
*service described herein and shall not create or extend in any manner whatsoever, any liability of ST.
*ST and the ST logo are trademarks or registered trademarks of ST in various countries.
*Information in this document supersedes and replaces all information previously supplied.
*The ST logo is a registered trademark of STMicroelectronics.
*All other names are the property of their respective owners.
*
*? 2006 STMicroelectronics - All rights reserved
*
*STMicroelectronics group of companies
*Australia - Belgium - Brazil - Canada - China - Czech Republic - Finland - France
*Germany - Hong Kong - India - Israel - Italy - Japan - Malaysia - Malta - Morocco
*Singapore - Spain - Sweden - Switzerland - United Kingdom - United States of America
*www.st.com
*
*******************************************************************
* POWER SCHOTTKY DIODE 15V TO 40V                           L60
*******************************************************************
* POWER SCHOTTKY DIODE 45V                                  L1455
*******************************************************************
* POWER SCHOTTKY DIODE 60V                                  L2845
*******************************************************************
* POWER SCHOTTKY DIODE 80V                                  L4275
*******************************************************************
* HIGH VOLTAGE POWER SCHOTTKY DIODE 100V TO 170V            L5230
*******************************************************************
* HIGH VOLTAGE POWER SCHOTTKY DIODE 200V       			    L8810
*******************************************************************

*******************************************************************
* POWER SCHOTTKY DIODE 15V TO 40V
*******************************************************************

*******************************************************************
* Model name       : STPS20L15D
* Description      : Low drop OR-ing power Schottky diode
* Package type     : TO220AC
*******************************************************************
.MODEL STPS20L15D D IS=200.00E-6 N=.7094 RS=3.6893E-3 IKF=.11957
+ EG=.69 XTI=2 CJO=4.7009E-9 M=.50334 VJ=.37311 ISR=203.63E-6
+ FC=0.5 NR=4.9950 TT=0
*$

*******************************************************************
* Model name       : STPS20L15G
* Description      : Low drop OR-ing power Schottky diode
* Package type     : D?PAK
*******************************************************************
*model STPS20L15G  anode
*				   | cathode
*				   | |
.subckt STPS20L15G 3 4
d1 3 4 dx
.model dx	D(IS=200.00E-6 N=.7094 RS=3.6893E-3 IKF=.11957 EG=.69 XTI=2 TT=0
+			  CJO=4.7009E-9 M=.50334 VJ=.37311 ISR=203.63E-6 FC=0.5 NR=4.9950 )

*	STMicroelectronics	case=D?PAK   Delivery= Tube
.ends

*******************************************************************
* Model name       : STPS40L15CW
* Description      : Low drop OR-ing power Schottky rectifier
* Package type     : TO247
*******************************************************************
*model STPS40L15CW  anode1
*				    | cathode
*				    | | anode2
*				    | | |
.subckt STPS40L15CW 1 2 3
d1 1 2 dx
d2 3 2 dx
.model dx	D(IS=200.00E-6 N=.7094 RS=3.6893E-3 IKF=.11957 EG=.69 XTI=2 CJO=4.7009E-9
+			M=.50334 VJ=.37311 ISR=203.63E-6 FC=0.5 NR=4.9950 TT=0)

*	STMicroelectronics	case=TO247   Delivery= Tube
.ends

*******************************************************************
* Model name       : STPS40L15CT
* Description      : Low drop OR-ing power Schottky rectifier
* Package type     : TO-220AB
*******************************************************************
*model STPS40L15CT  anode1
*				    | anode2
*				    | | cathode
*				    | | |
.subckt STPS40L15CT 1 2 3
d1 1 3 dx
d2 2 3 dx
.model dx	D(IS=200.00E-6 N=.7094 RS=3.6893E-3 IKF=.11957 EG=.69 XTI=2 CJO=4.7009E-9
+			M=.50334 VJ=.37311 ISR=203.63E-6 FC=0.5 NR=4.9950 TT=0)

*	STMicroelectronics	case=TO-220AB   Delivery= Tube
.ends

*******************************************************************
* Model name       : STPS120L15TV
* Description      : Low drop OR-ing power Schottky rectifier
* Package type     : ISOTOP
*******************************************************************
*model STPS120L15TV  anode1
*				     |  anode2
*				     |  |  cathode1
*				     |  |  |  cathode2
*				     |  |  |  |
.subckt STPS120L15TV A1 A2 K1 K2
d1 A1 K1 dx
d2 A2 K2 dx
.model dx	D(IS=975.85E-6 N=1.0264 RS=889.24E-6 IKF=1.0000E3 CJO=22.922E-9 XTI=2 EG=.69
+			M=.50618 VJ=.3905 ISR=443.69E-6 NR=4.9950 FC=0.5 TT=0)

*	STMicroelectronics	case=ISOTOP         Delivery= Tube
.ends

*******************************************************************
* Model name       : STPS0520M
* Description      : Power Schottky rectifier
* Package type     : STmite
*******************************************************************
.MODEL STPS0520M D IS=422.56E-9 N=1.0271 RS=18.686E-3 IKF=2.2722 CJO=496.68E-12
+ M=.46567 VJ=.3905 ISR=1.8281E-6 NR=4.9950 EG=.69 XTI=2 FC=0.5 TT=0
*$

*******************************************************************
* Model name       : STPS0520Z
* Description      : Power Schottky rectifier
* Package type     : SOD-123
*******************************************************************
.MODEL STPS0520Z D IS=5.6124E-6 N=.99911 RS=.13281 IKF=373.03 CJO=117.94E-12
+ M=.43891 VJ=1.0157 ISR=2.2120E-6 NR=4.9950 EG=.69 XTI=2 FC=0.5 TT=0
*$

*******************************************************************
* Model name       : 1N5817
* Description      : Low Drop Power Schottky Diode
* Package type     : DO-41
*******************************************************************
.MODEL 1N5817 D IS=698.22E-9 N=1.0015 RS=35.457E-3 IKF=6.0924 CJO=345.48E-12
+ M=.45399 VJ=.3905 ISR=2.0219E-6 NR=4.9950 EG=.69 XTI=2 TT=0 FC=0.5
*$

*******************************************************************
* Model name       : 1N5817RL
* Description      : Low Drop Power Schottky Diode
* Package type     : DO-41
*******************************************************************
.MODEL 1N5817RL D IS=698.22E-9 N=1.0015 RS=35.457E-3 IKF=6.0924 CJO=345.48E-12
+ M=.45399 VJ=.3905 ISR=2.0219E-6 NR=4.9950 EG=.69 XTI=2 TT=0 FC=0.5
*$

*******************************************************************
* Model name       : 1N5820
* Description      : Low Drop Power Schottky Diode
* Package type     : DO-201AD
*******************************************************************
.MODEL 1N5820 D IS=2.5069E-6 N=1.0281 RS=11.149E-3 IKF=403.32 CJO=980.33E-12
+ M=.47978 VJ=.3905 ISR=5.2260E-6 NR=4.9950 EG=.69 XTI=2 TT=0 FC=0.5
*$

*******************************************************************
* Model name       : 1N5820RL
* Description      : Low Drop Power Schottky Diode
* Package type     : DO-201AD
*******************************************************************
.MODEL 1N5820RL D IS=2.5069E-6 N=1.0281 RS=11.149E-3 IKF=403.32 CJO=980.33E-12
+ M=.47978 VJ=.3905 ISR=5.2260E-6 NR=4.9950 EG=.69 XTI=2 TT=0 FC=0.5
*$

*******************************************************************
* Model name       : STPS1L20M
* Description      : Low Drop Power Schottky Diode
* Package type     : DO-216AA
*******************************************************************
.MODEL STPS1L20M D IS=881.43E-9 N=.98951 RS=25.924E-3 IKF=1.0000E3 CJO=498.04E-12
+ M=.47478 VJ=.3905 ISR=998.50E-9 NR=4.9950 EG=.69 XTI=2 TT=0 FC=0.5
*$

*******************************************************************
* Model name       : STPS1L20MF
* Description      : Low Drop Power Schottky Diode
* Package type     : DO-216AA
*******************************************************************
.MODEL STPS1L20MF D IS=881.43E-9 N=.98951 RS=25.924E-3 IKF=1.0000E3 CJO=498.04E-12
+ M=.47478 VJ=.3905 ISR=998.50E-9 NR=4.9950 EG=.69 XTI=2 TT=0 FC=0.5
*$

*******************************************************************
* Model name       : STPS120M
* Description      : Low Drop Power Schottky Diode
* Package type     : DO-201AD
*******************************************************************
.MODEL STPS120M D IS=128.14E-9 N=1.0277 RS=18.697E-3 IKF=2.3143 CJO=482.21E-12
+ M=.48156 VJ=.3905 ISR=111.42E-9 NR=4.9950 EG=.69 XTI=2 TT=0 FC=0.5
*$
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
