wojciechk8/NVMemProg-hardware/fpga/Universal/data_fx_mux.vhd

library ieee;
use ieee.std_logic_1164.all;
use ieee.numeric_std.all;

entity DATA_FX_MUX is
  generic
  (
    NUM_MEM_PINS : natural
  );
  port
  (
    data_fx_mux_out : out std_logic;
    data_fx_mux_oe : out std_logic;
    data_dir : in std_logic;

    mem_pin_in : in std_logic_vector(NUM_MEM_PINS-1 downto 0); -- from mem to fx

    reg_select : in std_logic;
    reg_clk : in std_logic;
    reg_data_in : in std_logic_vector(5 downto 0)
  );
end DATA_FX_MUX;

architecture rtl of DATA_FX_MUX is

  -- Declare the register signal
  signal reg_num: std_logic_vector(5 downto 0);

  signal io_buf: std_logic;

begin

  -- Update the register output on the clock's rising edge
  process (reg_clk)
  begin
    if (rising_edge(reg_clk)) then
      if (reg_select = '1') then
        reg_num <= reg_data_in;
      end if;
    end if;
  end process;

  -- mux: select data_fx_mux from mem signals
  io_buf <= mem_pin_in(to_integer(unsigned(reg_num)));

  -- oe control logic
  data_fx_mux_out <= io_buf;
  data_fx_mux_oe <= not data_dir;

end rtl;
